neil-morrison44/dodecahedron-switch/src/model.h

#ifdef __has_attribute
#define HAVE_ATTRIBUTE(x) __has_attribute(x)
#else
#define HAVE_ATTRIBUTE(x) 0
#endif
#if HAVE_ATTRIBUTE(aligned) || (defined(__GNUC__) && !defined(__clang__))
#define DATA_ALIGN_ATTRIBUTE __attribute__((aligned(4)))
#else
#define DATA_ALIGN_ATTRIBUTE
#endif

const unsigned char model_data[] DATA_ALIGN_ATTRIBUTE = {
    0x28, 0x00, 0x00, 0x00, 0x54, 0x46, 0x4c, 0x33, 0x00, 0x00, 0x00, 0x00,
    0x00, 0x00, 0x00, 0x00, 0x00, 0x00, 0x00, 0x00, 0x00, 0x00, 0x12, 0x00,
    0x1c, 0x00, 0x04, 0x00, 0x08, 0x00, 0x0c, 0x00, 0x10, 0x00, 0x14, 0x00,
    0x00, 0x00, 0x18, 0x00, 0x12, 0x00, 0x00, 0x00, 0x03, 0x00, 0x00, 0x00,
    0xf0, 0x06, 0x00, 0x00, 0x28, 0x03, 0x00, 0x00, 0x10, 0x03, 0x00, 0x00,
    0x3c, 0x00, 0x00, 0x00, 0x04, 0x00, 0x00, 0x00, 0x01, 0x00, 0x00, 0x00,
    0x0c, 0x00, 0x00, 0x00, 0x08, 0x00, 0x0c, 0x00, 0x04, 0x00, 0x08, 0x00,
    0x08, 0x00, 0x00, 0x00, 0x08, 0x00, 0x00, 0x00, 0x09, 0x00, 0x00, 0x00,
    0x13, 0x00, 0x00, 0x00, 0x6d, 0x69, 0x6e, 0x5f, 0x72, 0x75, 0x6e, 0x74,
    0x69, 0x6d, 0x65, 0x5f, 0x76, 0x65, 0x72, 0x73, 0x69, 0x6f, 0x6e, 0x00,
    0x0a, 0x00, 0x00, 0x00, 0xc0, 0x02, 0x00, 0x00, 0xac, 0x02, 0x00, 0x00,
    0x80, 0x02, 0x00, 0x00, 0x3c, 0x02, 0x00, 0x00, 0x98, 0x01, 0x00, 0x00,
    0x64, 0x00, 0x00, 0x00, 0x58, 0x00, 0x00, 0x00, 0x44, 0x00, 0x00, 0x00,
    0x30, 0x00, 0x00, 0x00, 0x04, 0x00, 0x00, 0x00, 0xd2, 0xfc, 0xff, 0xff,
    0x04, 0x00, 0x00, 0x00, 0x10, 0x00, 0x00, 0x00, 0x31, 0x2e, 0x35, 0x2e,
    0x30, 0x00, 0x00, 0x00, 0x00, 0x00, 0x00, 0x00, 0x00, 0x00, 0x00, 0x00,
    0x00, 0x00, 0x00, 0x00, 0x00, 0x00, 0x00, 0x00, 0x00, 0x00, 0x00, 0x00,
    0xd0, 0xf9, 0xff, 0xff, 0x00, 0x00, 0x00, 0x00, 0x00, 0x00, 0x00, 0x00,
    0x00, 0x00, 0x00, 0x00, 0xe0, 0xf9, 0xff, 0xff, 0x00, 0x00, 0x00, 0x00,
    0x00, 0x00, 0x00, 0x00, 0x00, 0x00, 0x00, 0x00, 0xf0, 0xf9, 0xff, 0xff,
    0x00, 0x00, 0x00, 0x00, 0x22, 0xfd, 0xff, 0xff, 0x04, 0x00, 0x00, 0x00,
    0x20, 0x01, 0x00, 0x00, 0x4f, 0x5b, 0xc8, 0x3e, 0xe7, 0xd7, 0xf2, 0xbe,
    0xce, 0xcf, 0x25, 0xbe, 0x18, 0x95, 0x2e, 0xbf, 0x32, 0x65, 0x84, 0xbe,
    0xdc, 0xd6, 0xba, 0xbe, 0x33, 0xde, 0xd3, 0xba, 0x76, 0x44, 0xb2, 0xbe,
    0x05, 0xa4, 0x10, 0xbf, 0x2e, 0x6c, 0xae, 0x3d, 0xa9, 0xd2, 0xcb, 0x3d,
    0xf0, 0xbb, 0xf3, 0x3e, 0xda, 0x82, 0xec, 0xbe, 0x76, 0xcb, 0xf6, 0xbe,
    0x98, 0xf7, 0xe2, 0xbe, 0x93, 0xf7, 0xb9, 0xbe, 0x78, 0xea, 0x63, 0x3e,
    0xa2, 0xdc, 0x03, 0xbe, 0x18, 0xdc, 0x11, 0xbe, 0xb1, 0xfc, 0x0d, 0xbf,
    0x0d, 0x04, 0x30, 0x3e, 0x88, 0x0f, 0xdc, 0xbd, 0x72, 0x21, 0xb1, 0x3e,
    0x24, 0xdf, 0x4b, 0xbf, 0x92, 0x4e, 0x80, 0x3e, 0x4d, 0xfc, 0x3d, 0xbe,
    0x9c, 0x15, 0xc5, 0x3e, 0x36, 0xab, 0xf2, 0xbc, 0x84, 0x9f, 0x07, 0x3f,
    0x09, 0x4e, 0xd9, 0xbe, 0x1b, 0x47, 0x32, 0x3f, 0xea, 0xeb, 0x05, 0x3e,
    0x7a, 0xde, 0x62, 0xbe, 0x1c, 0x1e, 0x19, 0xbe, 0xbe, 0x77, 0x5c, 0xbc,
    0x3e, 0x47, 0x1e, 0x3e, 0x29, 0x5b, 0x9c, 0x3e, 0x93, 0x40, 0x95, 0x3e,
    0x99, 0xf6, 0x99, 0xbe, 0x4a, 0xf5, 0xf7, 0x3e, 0xd1, 0x1a, 0xf1, 0xbe,
    0x0f, 0x2d, 0x95, 0x3d, 0xd6, 0x63, 0x16, 0xbf, 0x1c, 0x48, 0x42, 0x3e,
    0x4c, 0xc9, 0x9d, 0xbe, 0x8b, 0xf5, 0xf8, 0x3d, 0x13, 0x0e, 0x4b, 0xbe,
    0xb7, 0xfa, 0x9c, 0x3e, 0xd8, 0x62, 0x0e, 0xbf, 0x6d, 0x57, 0x50, 0x3a,
    0x30, 0xbe, 0x95, 0xbe, 0x0c, 0xed, 0xb6, 0xbc, 0x36, 0x26, 0x64, 0x3e,
    0x80, 0x29, 0x1f, 0xbf, 0x5b, 0xb7, 0x5a, 0xbe, 0x89, 0xfa, 0xf9, 0x3e,
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
const int model_data_len = 1872;
